iotdevspot/ws2812-leds-on-a-heart-shaped-pcb/images/1.PNG

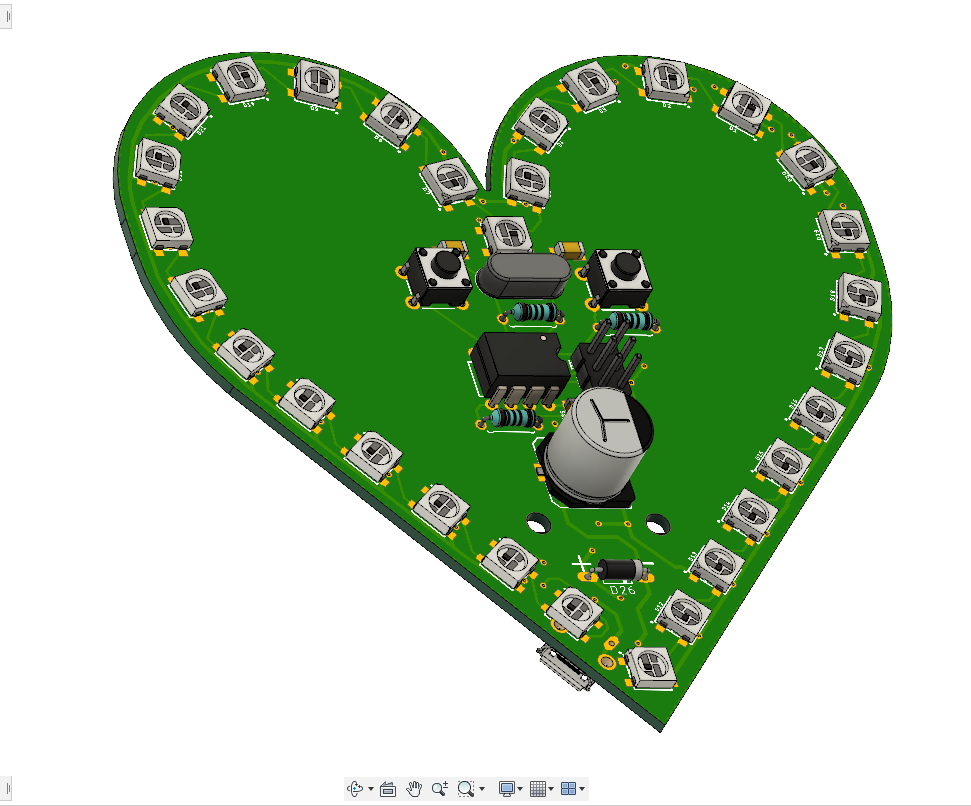
images/1.PNG
