iotdevspot/ws2812-leds-on-a-heart-shaped-pcb/images/2.PNG

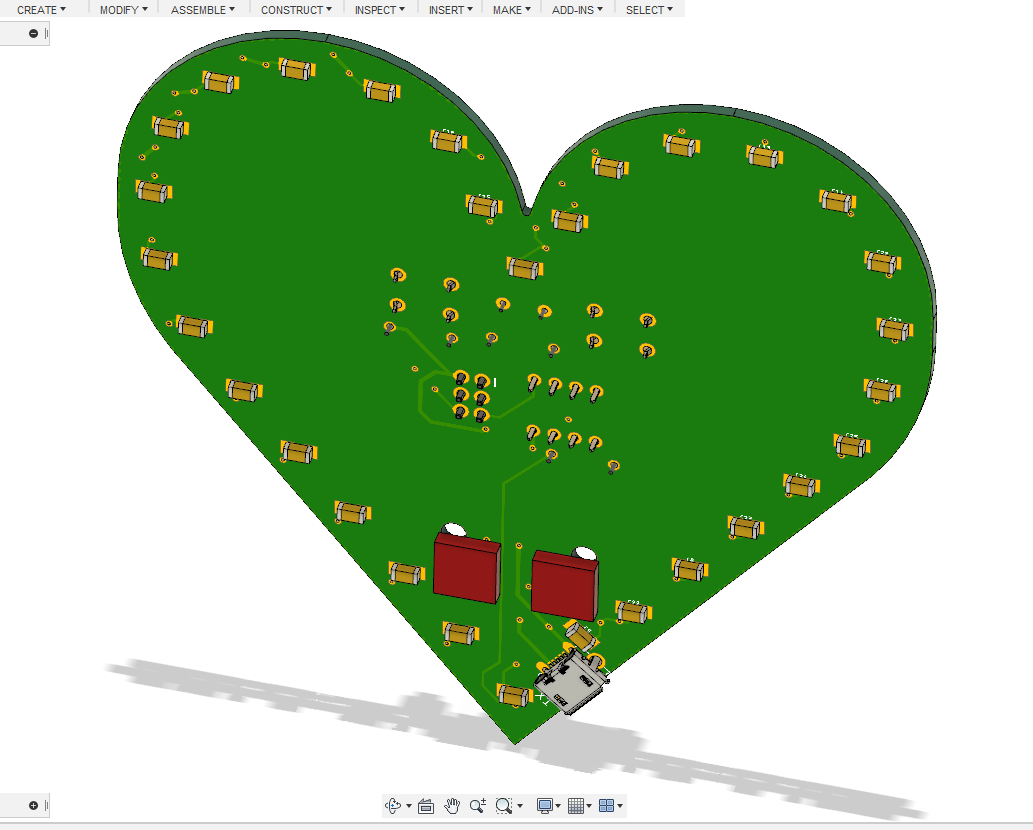
images/2.PNG
