iotdevspot/ws2812-leds-on-a-heart-shaped-pcb/images/3.PNG

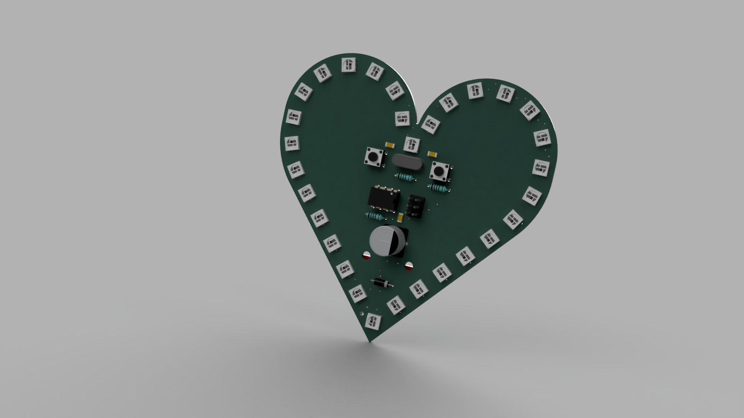
images/3.PNG
