iotdevspot/ws2812-leds-on-a-heart-shaped-pcb/images/4.PNG

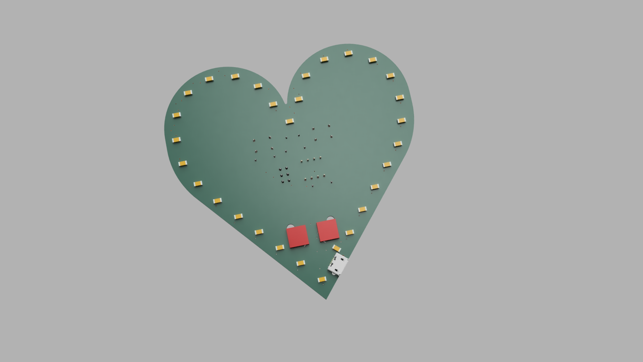
images/4.PNG
