iotdevspot/ws2812-leds-on-a-heart-shaped-pcb/images/5.png

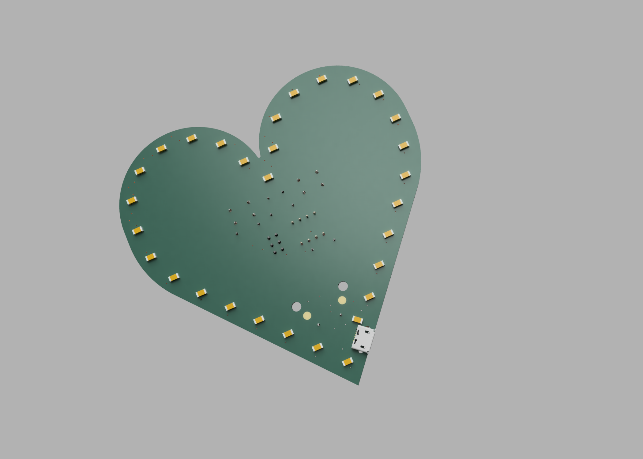
images/5.png
