iotdevspot/ws2812-leds-on-a-heart-shaped-pcb/images/6.png

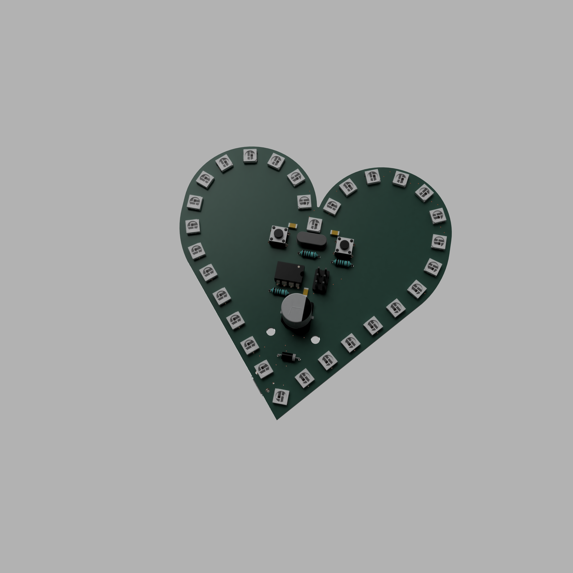
images/6.png
