iotdevspot/ws2812-leds-on-a-heart-shaped-pcb/images/8.PNG

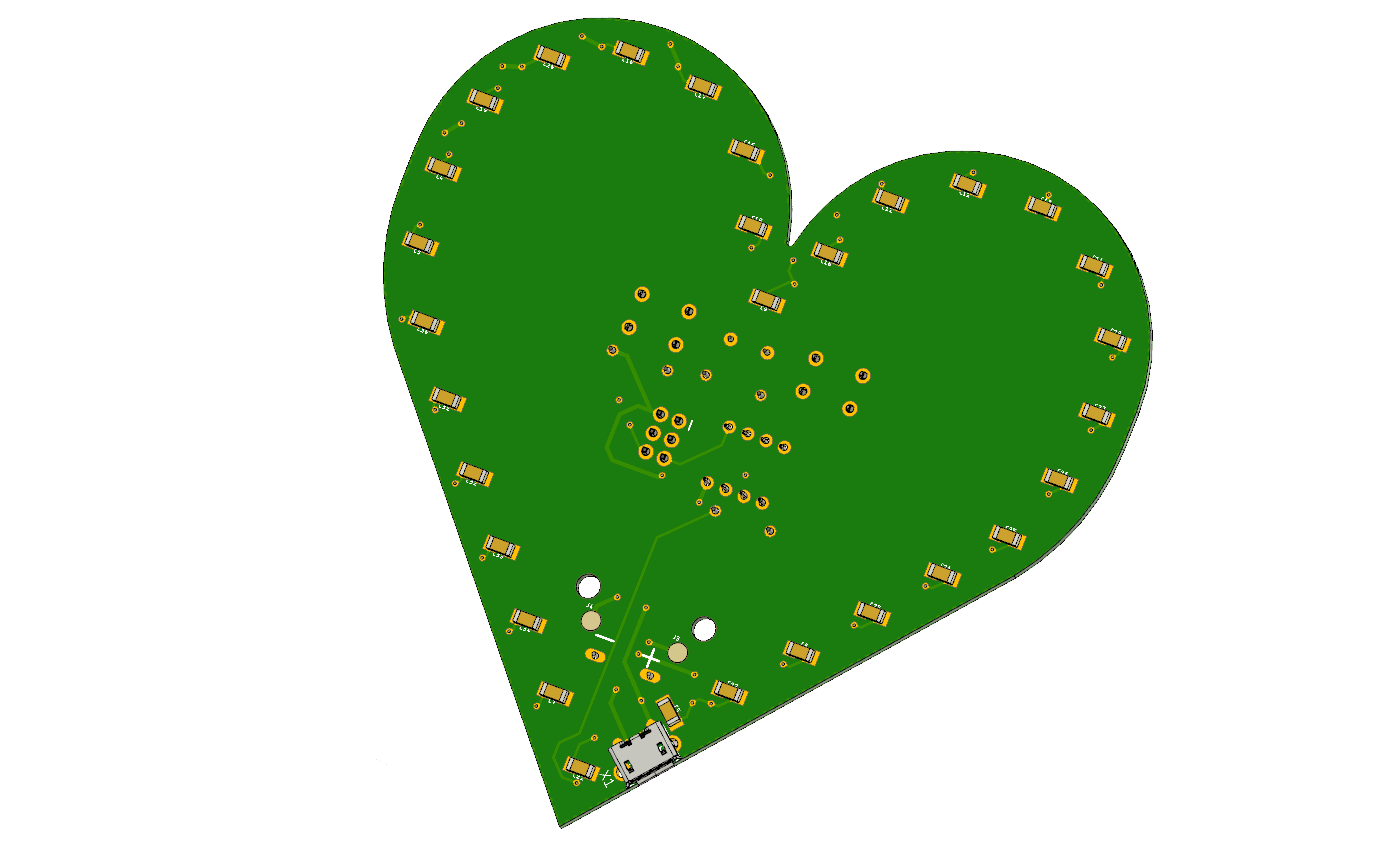
images/8.PNG
